kmcgain/Pedalboard/docs/arduino_dc_in.jpg

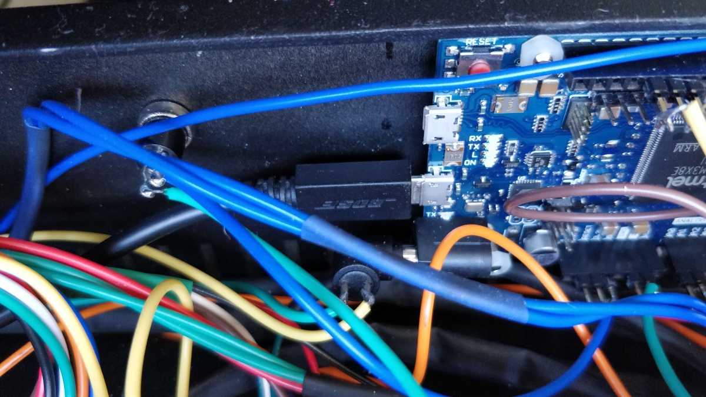
docs/arduino_dc_in.jpg
