kmcgain/Pedalboard/docs/arduino_due.png

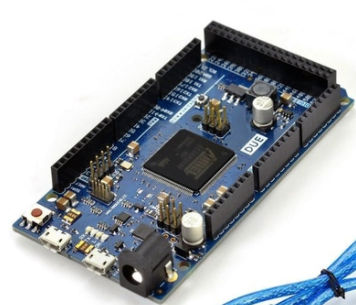
docs/arduino_due.png
