kmcgain/Pedalboard/docs/arduino_side.jpg

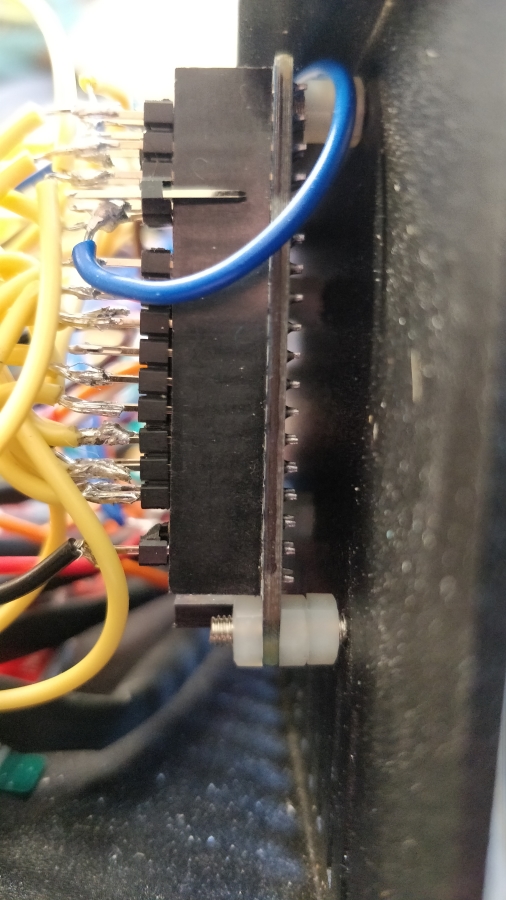
docs/arduino_side.jpg
