kmcgain/Pedalboard/docs/breadboard.png

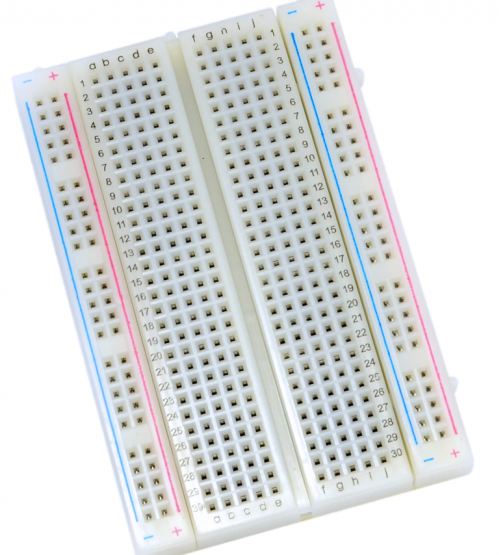
docs/breadboard.png
