kmcgain/Pedalboard/docs/dc_socket.png

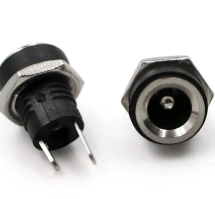
docs/dc_socket.png
