kmcgain/Pedalboard/docs/din_socket.png

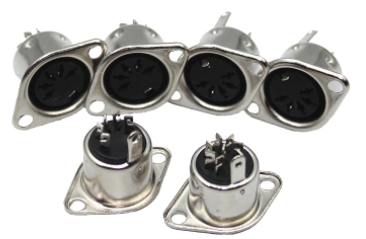
docs/din_socket.png
