kmcgain/Pedalboard/docs/dupont.png

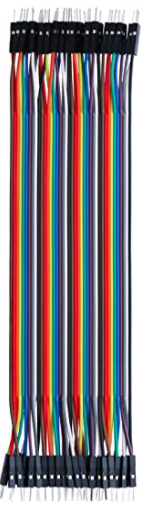
docs/dupont.png
