kmcgain/Pedalboard/docs/enclosure_midi.png

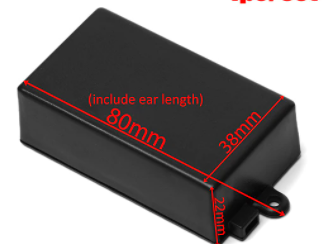
docs/enclosure_midi.png
