kmcgain/Pedalboard/docs/exp_socket.jpg

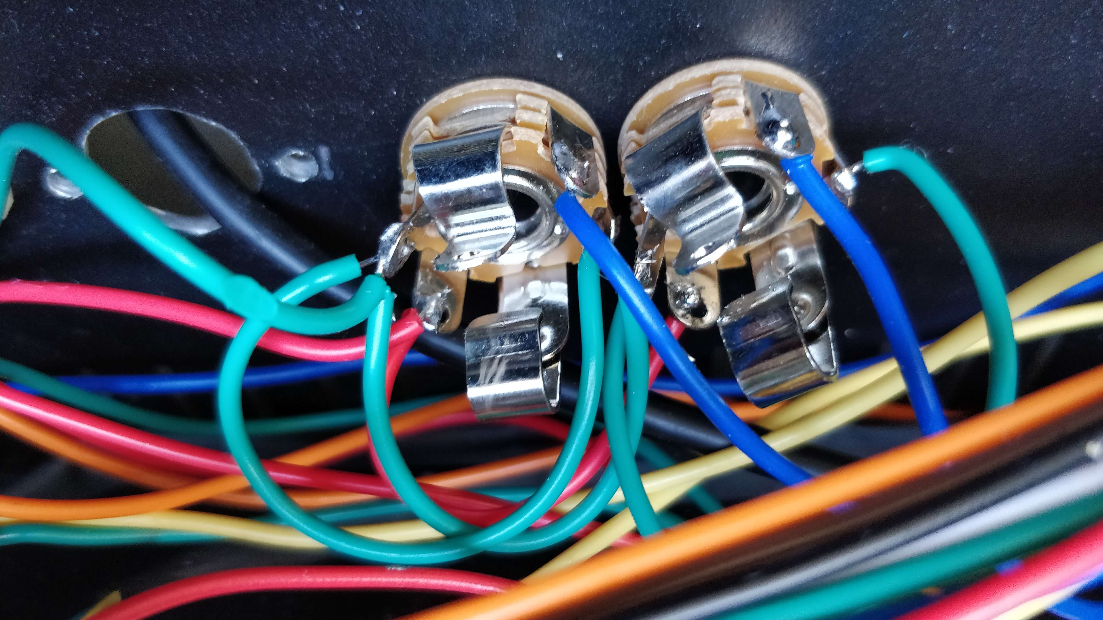
docs/exp_socket.jpg
