kmcgain/Pedalboard/docs/footswitch.png

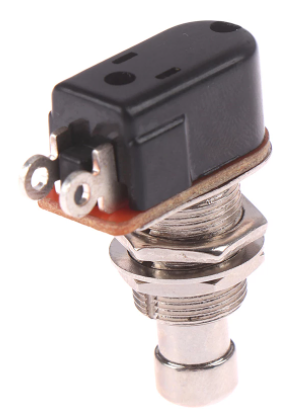
docs/footswitch.png
