kmcgain/Pedalboard/docs/fs_pins.jpg

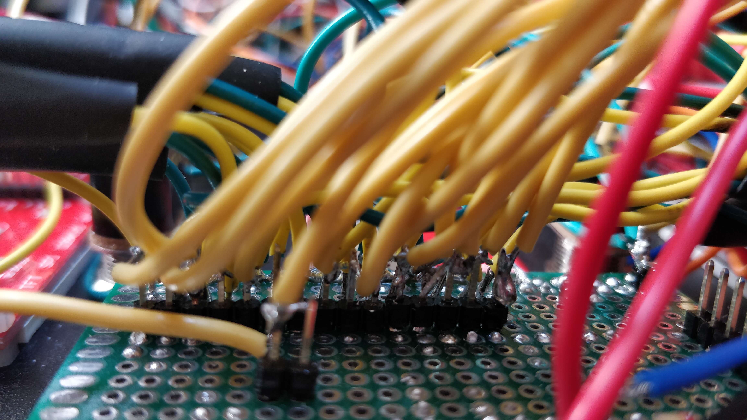
docs/fs_pins.jpg
