kmcgain/Pedalboard/docs/ground_pcb.jpg

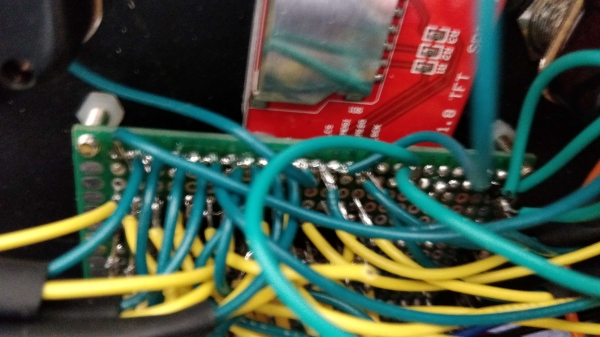
docs/ground_pcb.jpg
