kmcgain/Pedalboard/docs/hammond.png

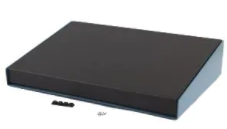
docs/hammond.png
