kmcgain/Pedalboard/docs/led.jpg

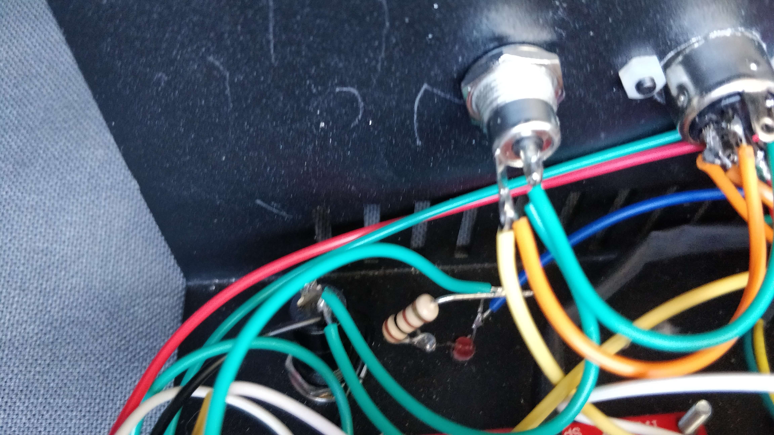
docs/led.jpg
