kmcgain/Pedalboard/docs/midi_box.jpg

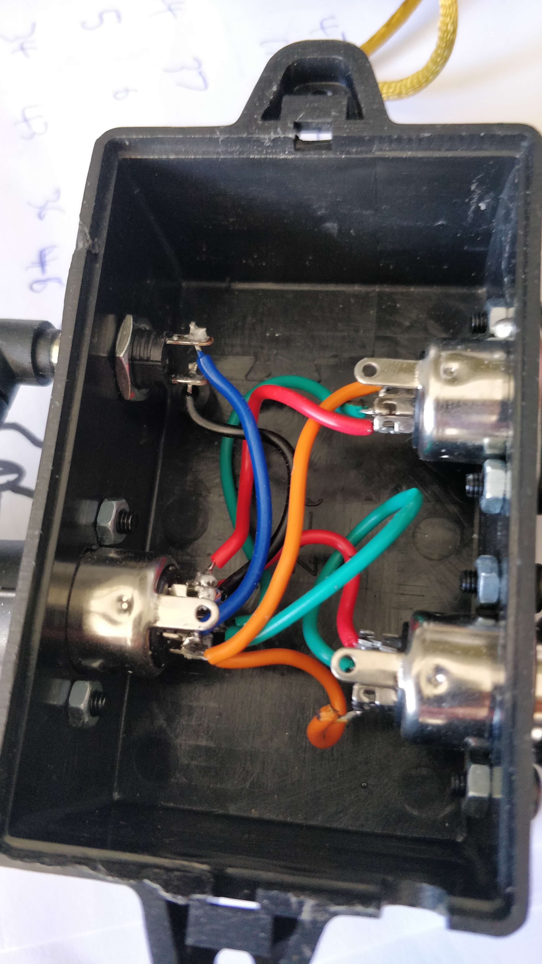
docs/midi_box.jpg
