kmcgain/Pedalboard/docs/midi_dc_in.jpg

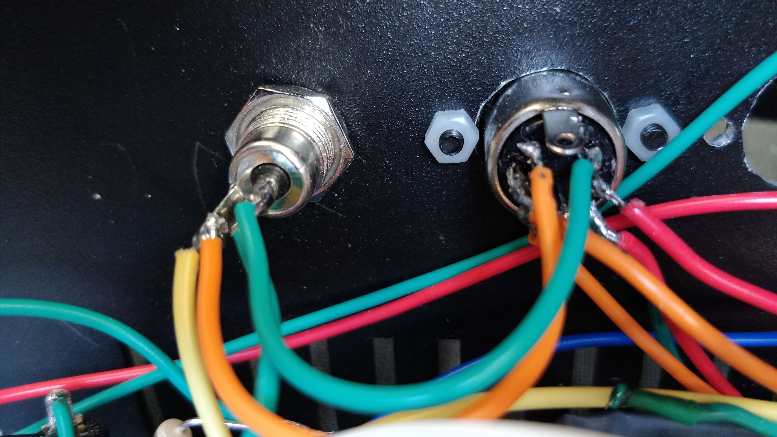
docs/midi_dc_in.jpg
