kmcgain/Pedalboard/docs/midi_dc_in_2.jpg

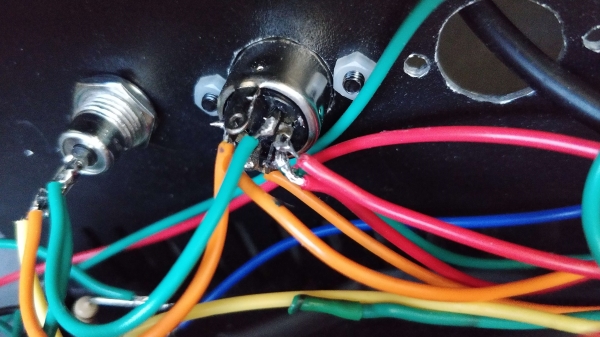
docs/midi_dc_in_2.jpg
