kmcgain/Pedalboard/docs/midi_resistor.jpg

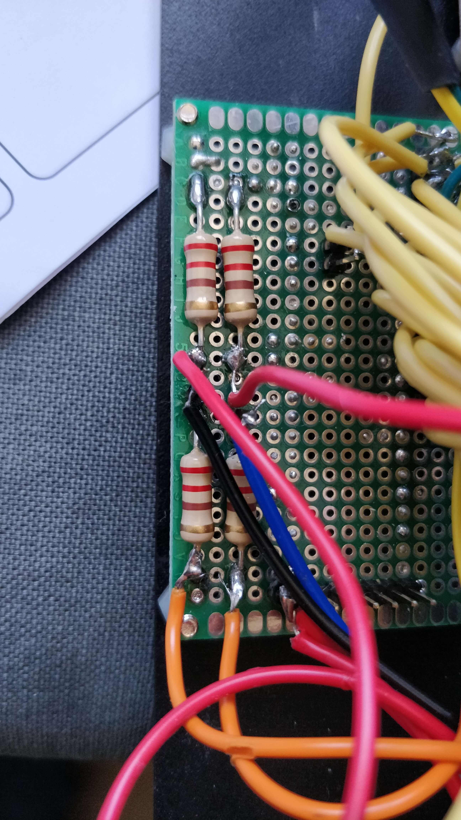
docs/midi_resistor.jpg
