kmcgain/Pedalboard/docs/pcb_board.png

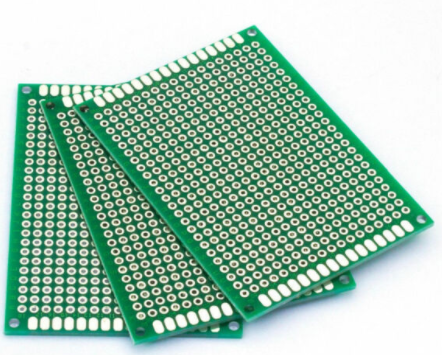
docs/pcb_board.png
