kmcgain/Pedalboard/docs/plastic_nut.png

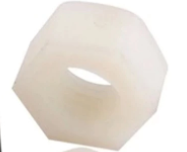
docs/plastic_nut.png
