kmcgain/Pedalboard/docs/screen_pcb.jpg

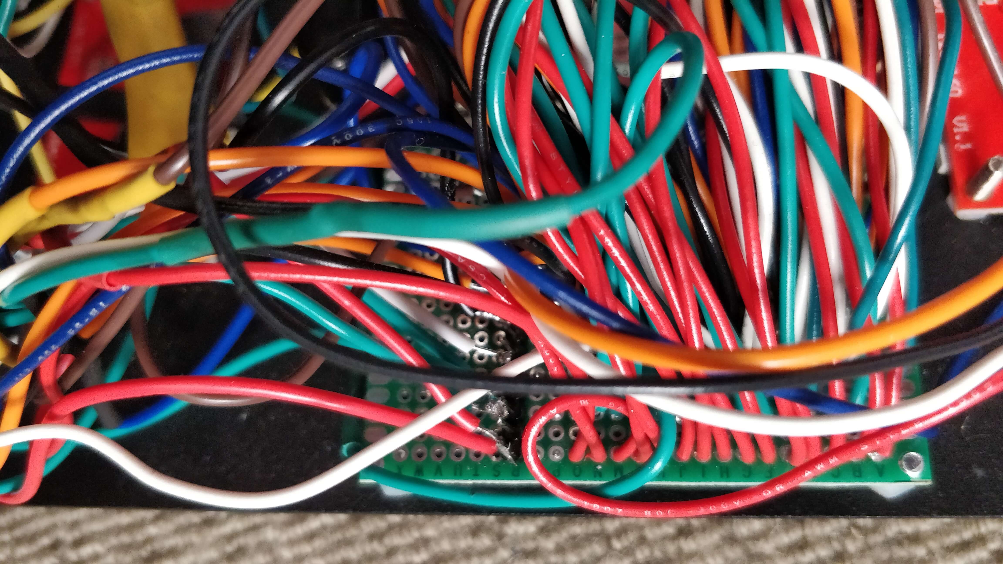
docs/screen_pcb.jpg
