kmcgain/Pedalboard/docs/screen_placement.png

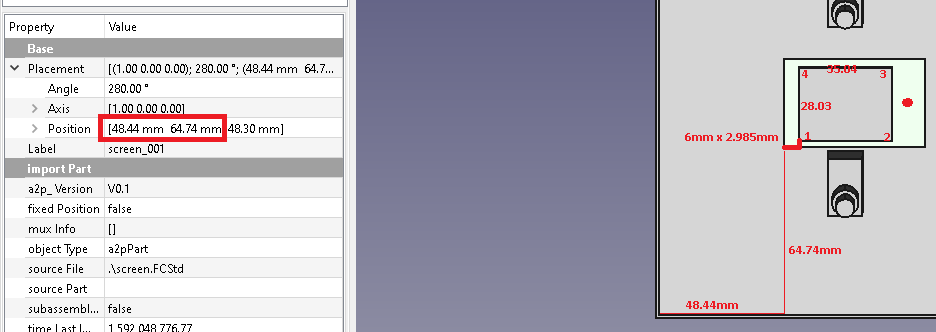
docs/screen_placement.png
