kmcgain/Pedalboard/docs/screen_side.jpg

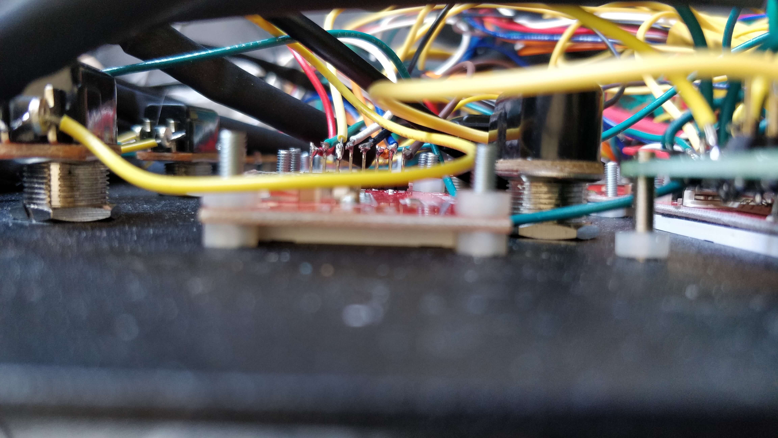
docs/screen_side.jpg
