kmcgain/Pedalboard/docs/screws.png

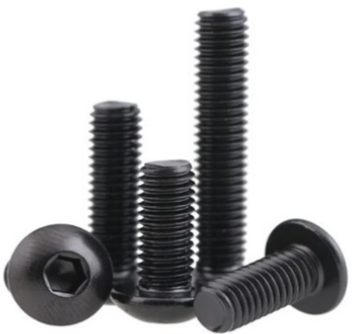
docs/screws.png
