kmcgain/Pedalboard/docs/spi_header.png

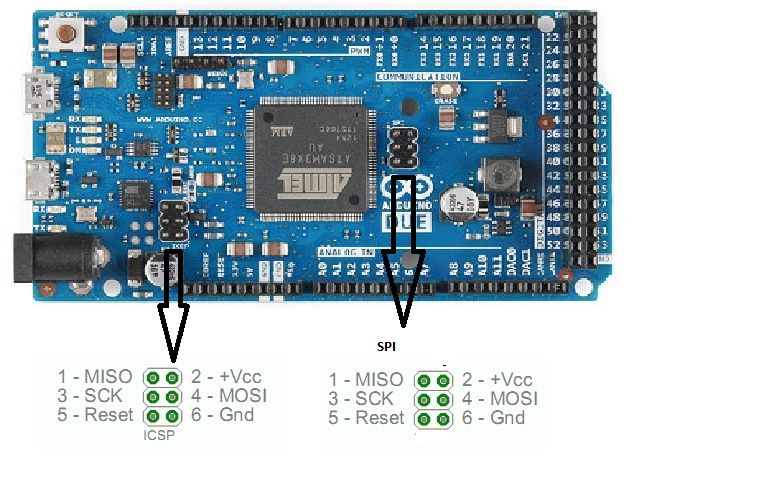
docs/spi_header.png
