kmcgain/Pedalboard/docs/switch_latching.png

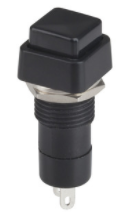
docs/switch_latching.png
