kmcgain/Pedalboard/docs/switch_momentary.png

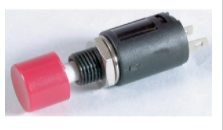
docs/switch_momentary.png
