kmcgain/Pedalboard/docs/tft_screen.png

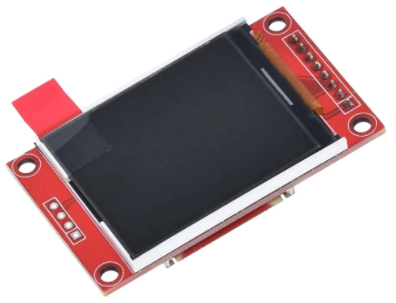
docs/tft_screen.png
