kmcgain/Pedalboard/docs/trs_socket.png

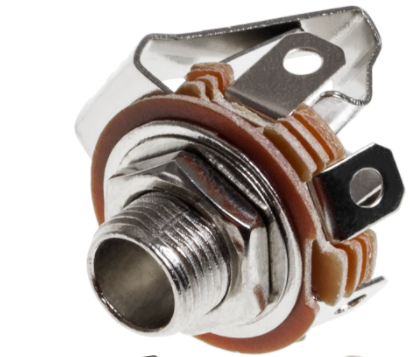
docs/trs_socket.png
