kmcgain/Pedalboard/docs/usb_socket.png

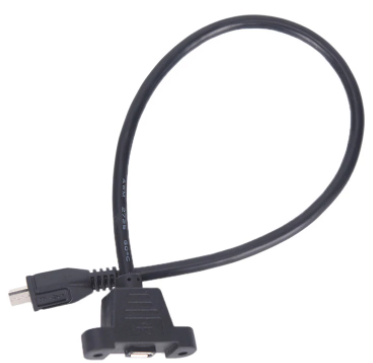
docs/usb_socket.png
