kmcgain/Pedalboard/docs/volt_pins.jpg

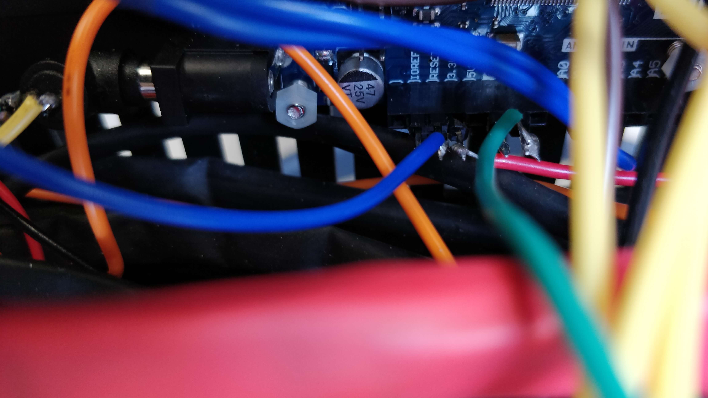
docs/volt_pins.jpg
