kmcgain/Pedalboard/docs/solder_bridge.png

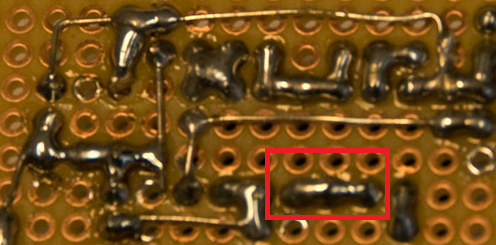
docs/solder_bridge.png
