kmcgain/Pedalboard/src/Pedalboard/Display/tft_screen.h

#pragma once


#include "../../Domain/screen.h"
#include "../../Domain/function/function.h"
#include "../../Domain/function/state/function_state.h"

#include "../../Domain/preset.h"
#include "../../Domain/tuner.h"


#include <TFT_eSPI.h>
#include <SPI.h>

class TftScreen : public Screen {
private:
	int screenNumber;
	int cs_pin;

public: 
	TftScreen(byte screenNumber);
	static void GlobalInit();
	virtual void Init();
	virtual void DisplayFunction(FunctionState* functionState, Preset* currentPreset, TunerData& tuner);
	virtual void SetToWrite();
	virtual void SetToNotWrite();	
};
