kmcgain/Pedalboard/Test/pch.cpp

//
// pch.cpp
// Include the standard header and generate the precompiled header.
//

#include "pch.h"
//
//#include "D:/src/c++/library/googletest-release-1.10.0/googlemock/src/gmock-cardinalities.cc"
//#include "D:/src/c++/library/googletest-release-1.10.0/googlemock/src/gmock-internal-utils.cc"
//#include "D:/src/c++/library/googletest-release-1.10.0/googlemock/src/gmock-matchers.cc"
////#include "D:/src/c++/library/googletest-release-1.10.0/googlemock/src/gmock-spec-builders.cc"
//#include "D:/src/c++/library/googletest-release-1.10.0/googlemock/src/gmock.cc"
